michal2229/g27_emu/kicad/g27_emu/g27_emu.kicad_sch

## KiCad design kicad/g27_emu/g27_emu.kicad_sch (2024-10-26)

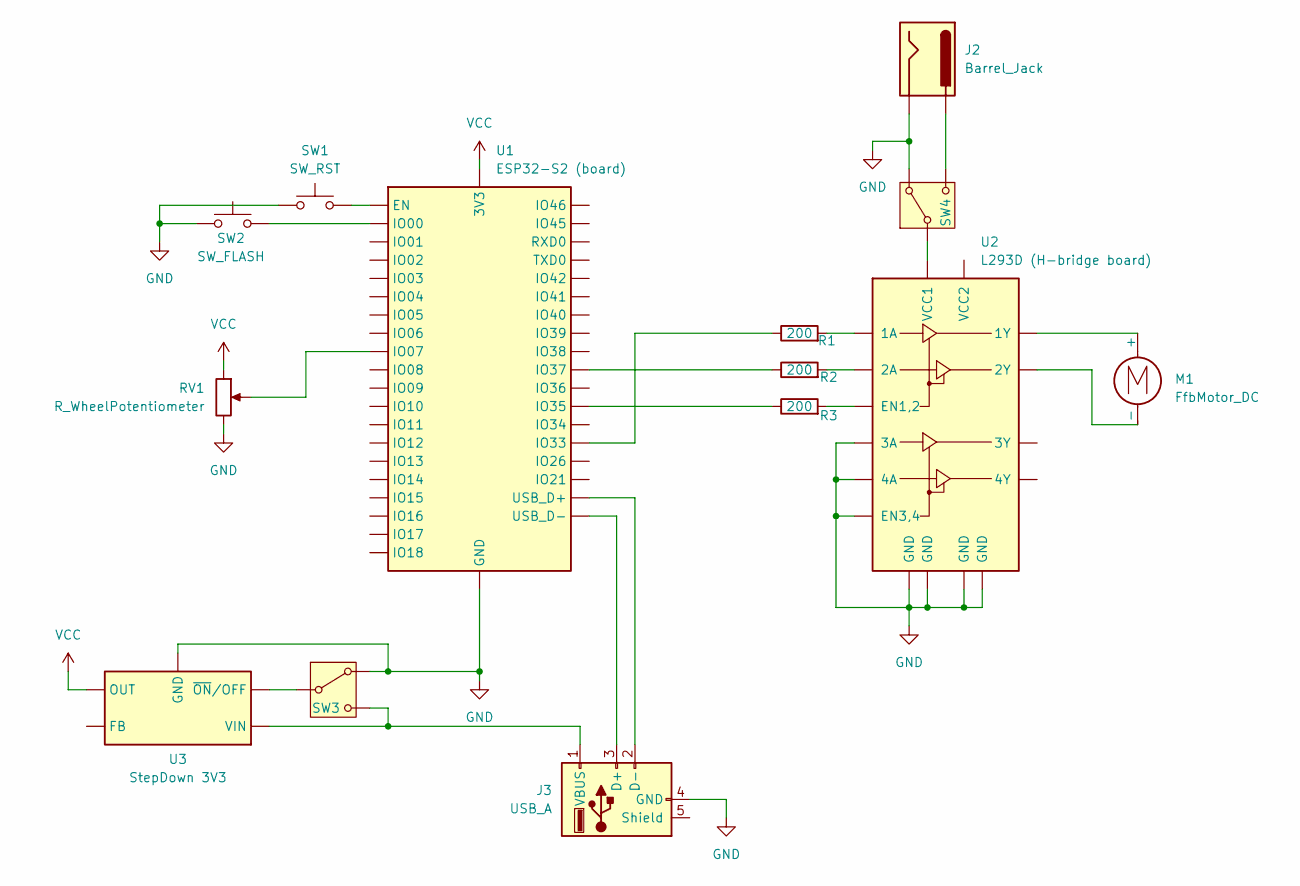
[picture p3: schematic g27_emu.kicad_sch]

Parts:
J2: Barrel_Jack
J3: USB_A
M1: FfbMotor_DC
R1, R2, R3: 200
RV1: R_WheelPotentiometer
SW1: SW_RST
SW2: SW_FLASH
SW3, SW4: Nidec_Copal_CAS-120A
U1: ESP32-S2 (board); ESP32-S2-WROVER
U2: L293D (H-bridge board); DIP-16_W7.62mm
U3: StepDown 3V3; TO-263-5_TabPin3

Connections:
GND: J2.2, J3.4 (GND), RV1.3, SW1.1, SW2.1, SW3.3 (A), SW4.3 (A), U1.1 (GND), U1.26 (GND), U1.42 (GND), U1.43 (GND), U2.4 (GND), U2.5 (GND), U2.9 (EN3,4), U2.10 (3A), U2.12 (GND), U2.13 (GND), U2.15 (4A), U3.3 (GND)
unnamed: J2.1, SW4.1 (C)
unnamed: J3.1 (VBUS), SW3.1 (C), U3.1 (VIN)
unnamed: J3.2 (D-), U1.23 (USB_D+)
unnamed: J3.3 (D+), U1.22 (USB_D-)
unnamed: M1.1 (+), U2.3 (1Y)
unnamed: M1.2 (-), U2.6 (2Y)
unnamed: R1.1, U1.27 (IO33)
unnamed: R1.2, U2.2 (1A)
unnamed: R2.1, U1.31 (IO37)
unnamed: R2.2, U2.7 (2A)
unnamed: R3.1, U1.29 (IO35)
unnamed: R3.2, U2.1 (EN1,2)
unnamed: RV1.2, U1.10 (IO07)
unnamed: SW1.2, U1.41 (EN)
unnamed: SW2.2, U1.3 (IO00)
unnamed: SW3.2 (B), U3.5 (~ON/OFF)
unnamed: SW4.2 (B), U2.16 (VCC1)
VCC: RV1.1, U1.2 (3V3), U3.2 (OUT)
